ctrlh/solder-alert/firmware/images/btn-nogo.png

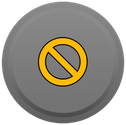
firmware/images/btn-nogo.png
