ctrlh/solder-alert/firmware/images/btn-power-off.png

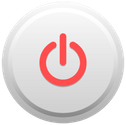
firmware/images/btn-power-off.png
