ctrlh/solder-alert/assembly/full/assembly-01.webp

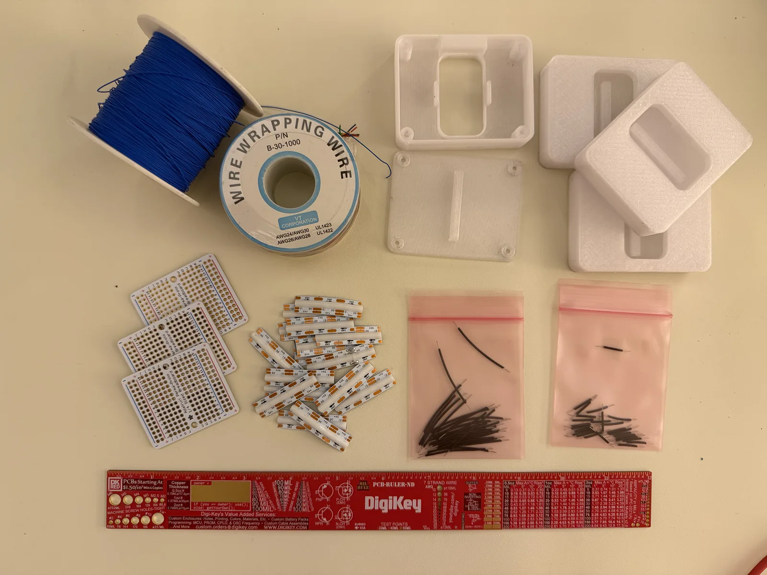
assembly/full/assembly-01.webp
