ctrlh/solder-alert/assembly/full/assembly-02.webp

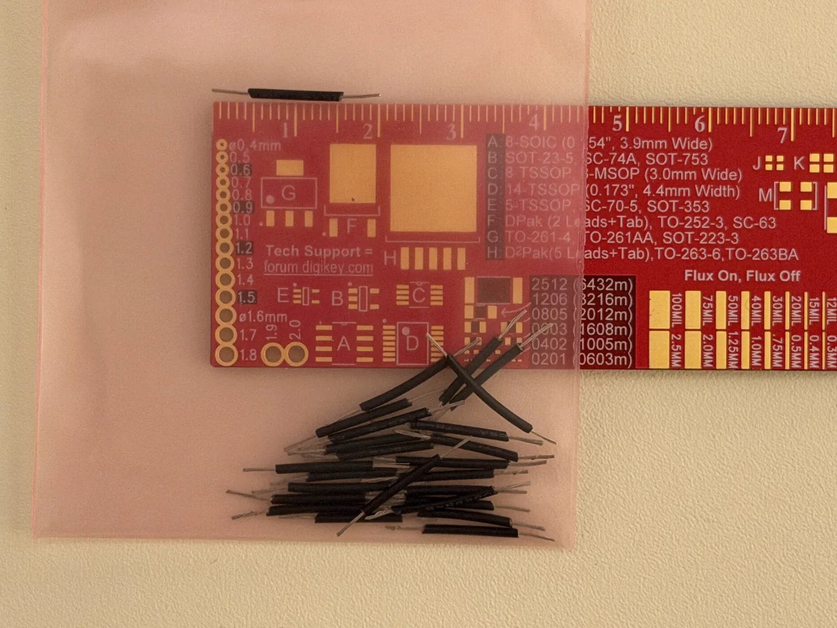
assembly/full/assembly-02.webp
