ctrlh/solder-alert/assembly/full/assembly-03.webp

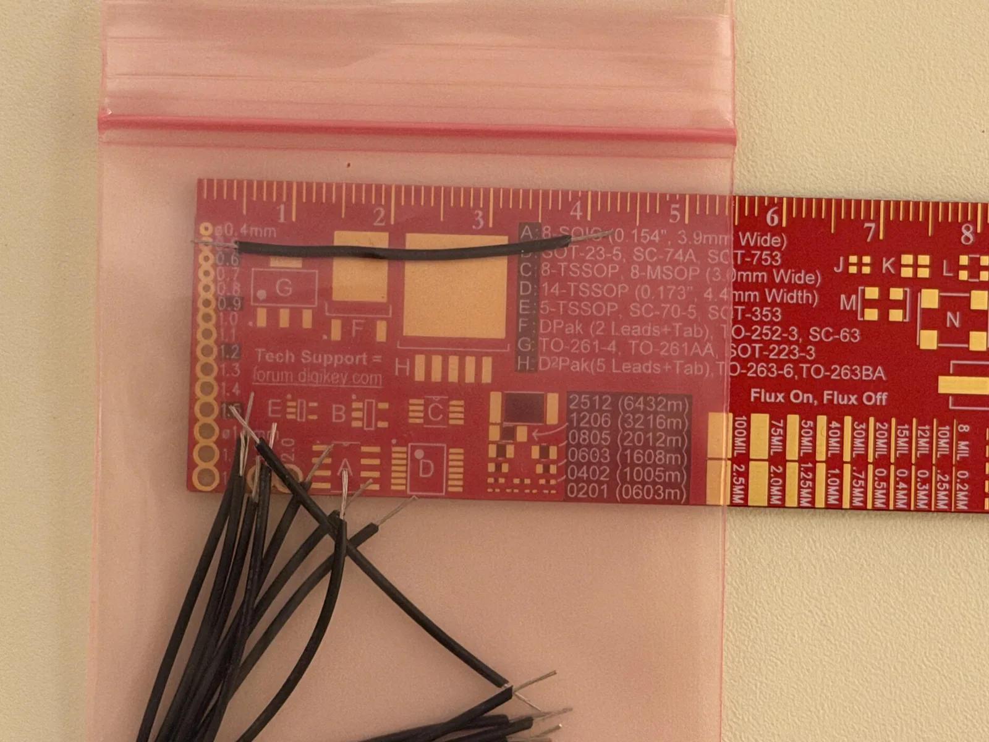
assembly/full/assembly-03.webp
