ctrlh/solder-alert/assembly/full/assembly-05.webp

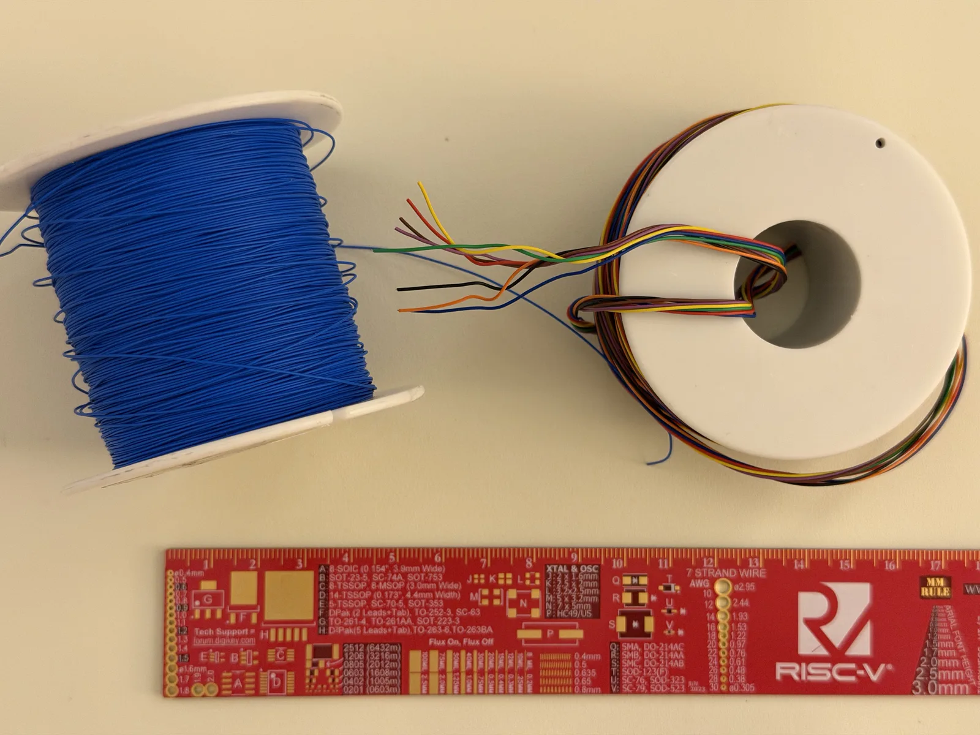
assembly/full/assembly-05.webp
