ctrlh/solder-alert/assembly/full/assembly-06.webp

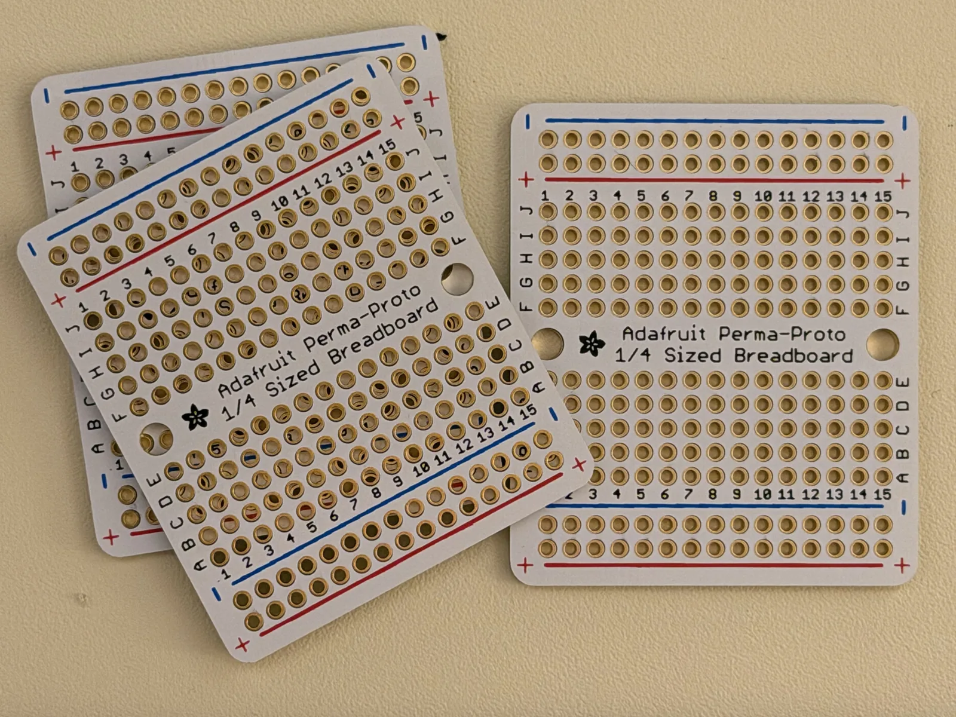
assembly/full/assembly-06.webp
