ctrlh/solder-alert/assembly/full/assembly-07.webp

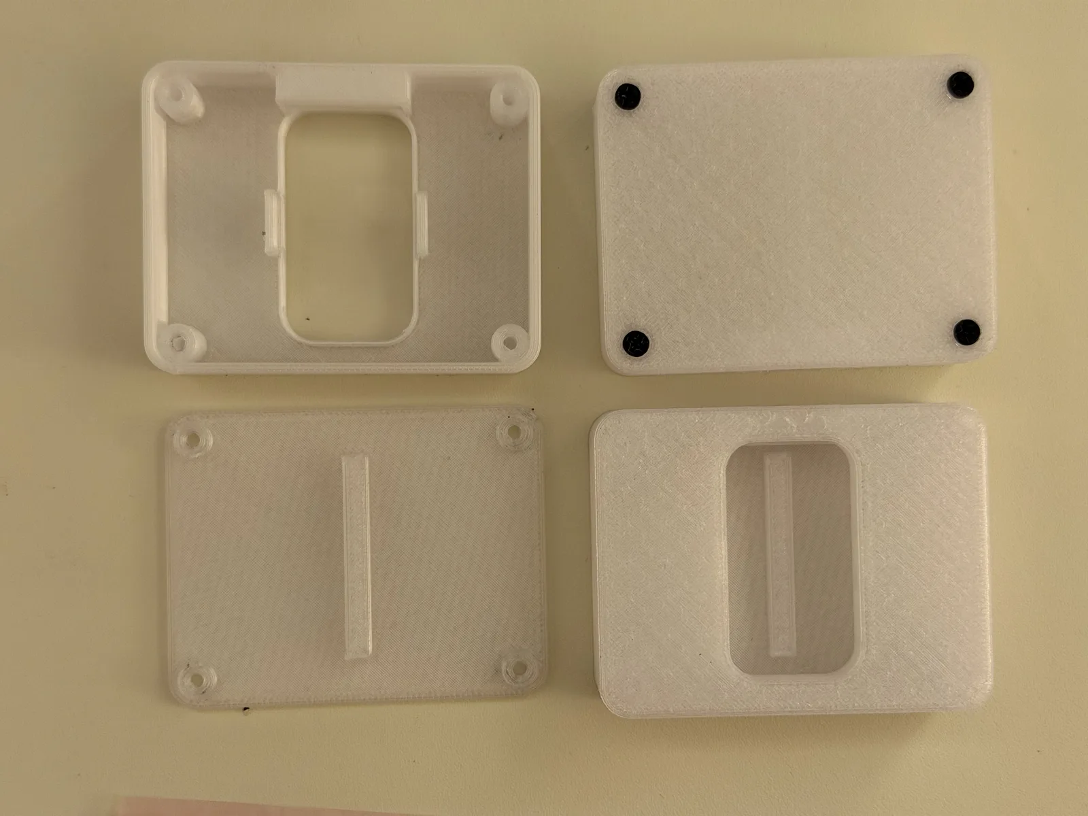
assembly/full/assembly-07.webp
