ctrlh/solder-alert/assembly/full/assembly-08.webp

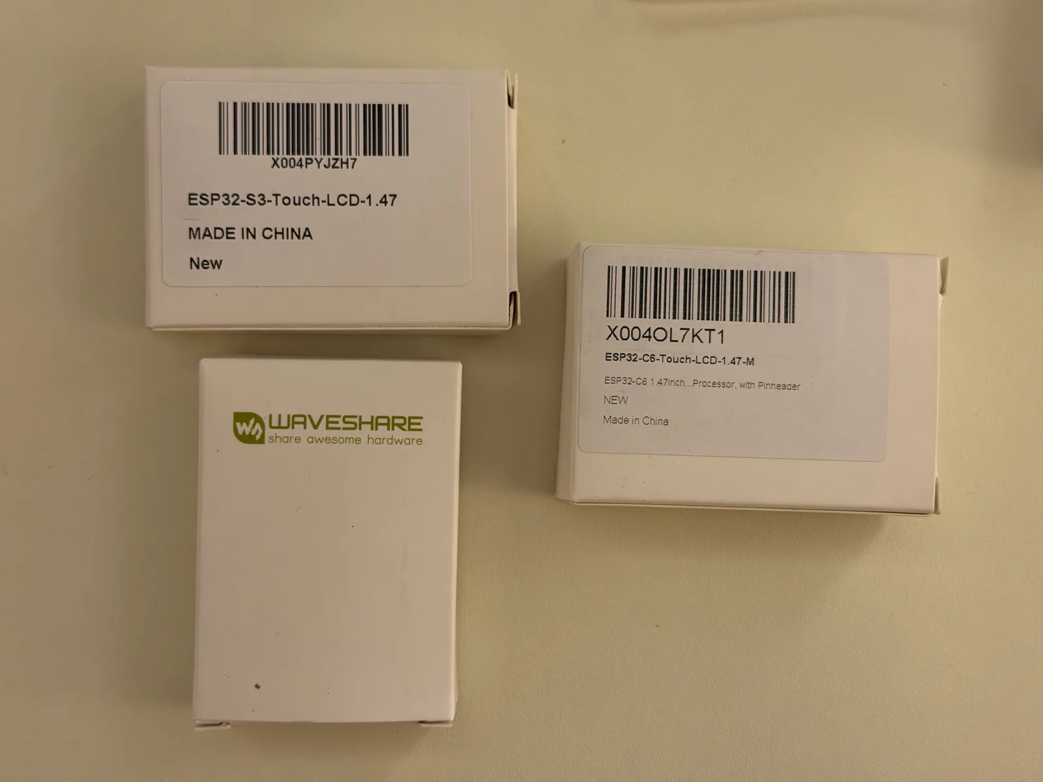
assembly/full/assembly-08.webp
