ctrlh/solder-alert/assembly/full/assembly-09.webp

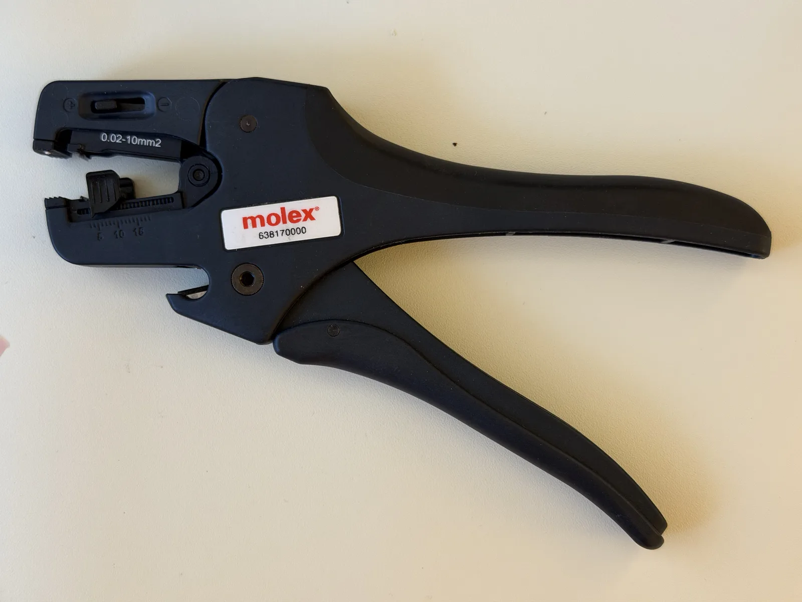
assembly/full/assembly-09.webp
