ctrlh/solder-alert/assembly/full/assembly-10.webp

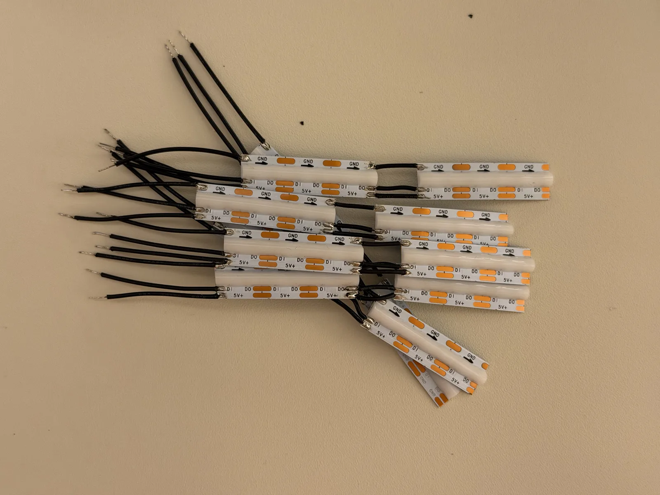
assembly/full/assembly-10.webp
