ctrlh/solder-alert/assembly/full/assembly-11.webp

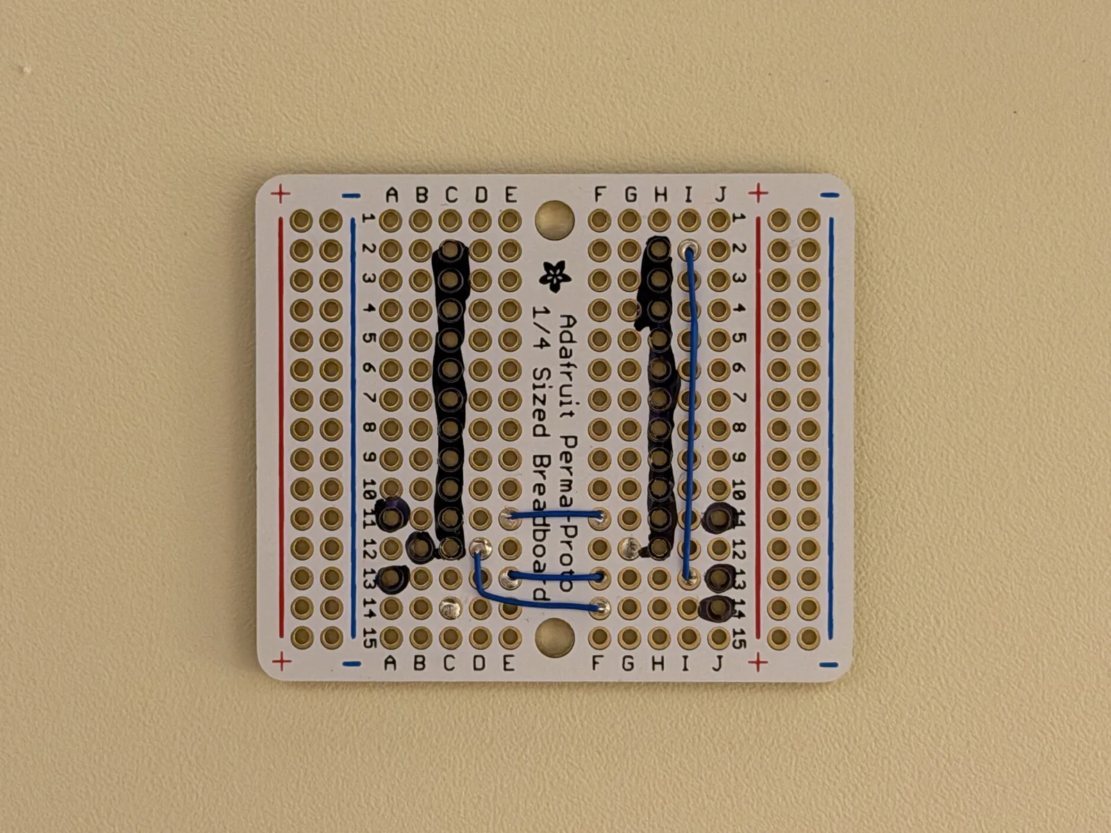
assembly/full/assembly-11.webp
