ctrlh/solder-alert/assembly/full/assembly-12.webp

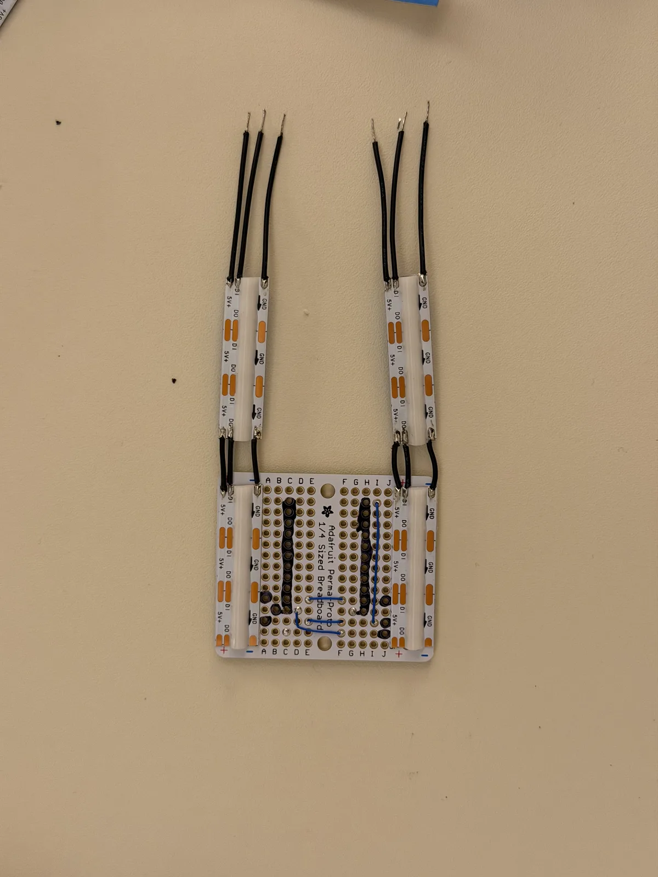
assembly/full/assembly-12.webp
