ctrlh/solder-alert/assembly/full/assembly-14.webp

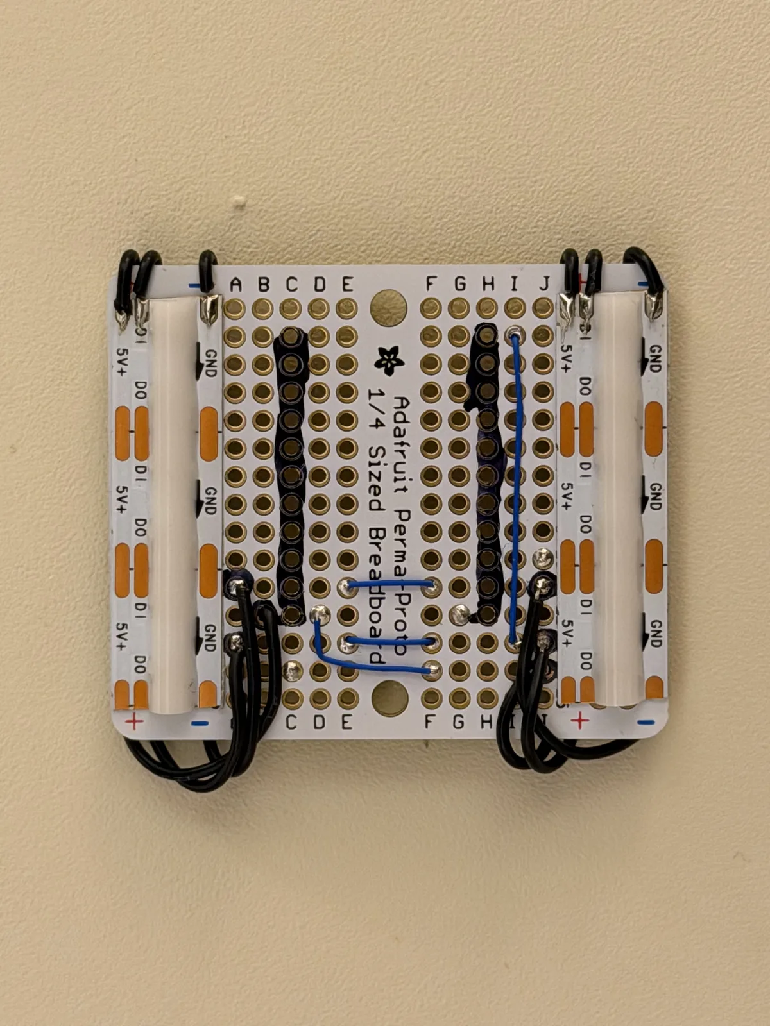
assembly/full/assembly-14.webp
