ctrlh/solder-alert/assembly/full/assembly-17.webp

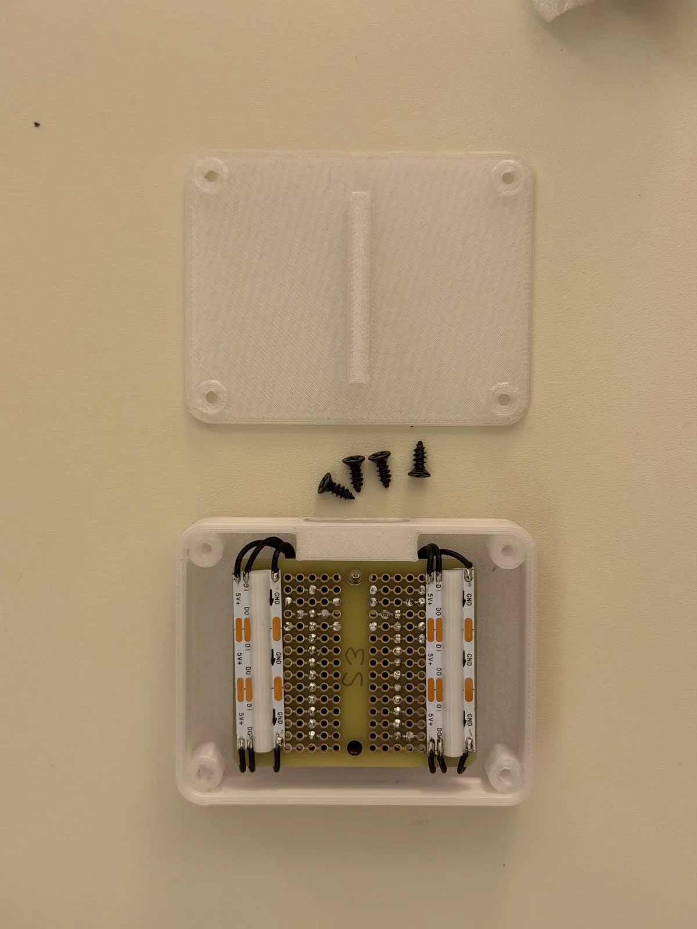
assembly/full/assembly-17.webp
