ctrlh/solder-alert/assembly/full/wire-thickness.webp

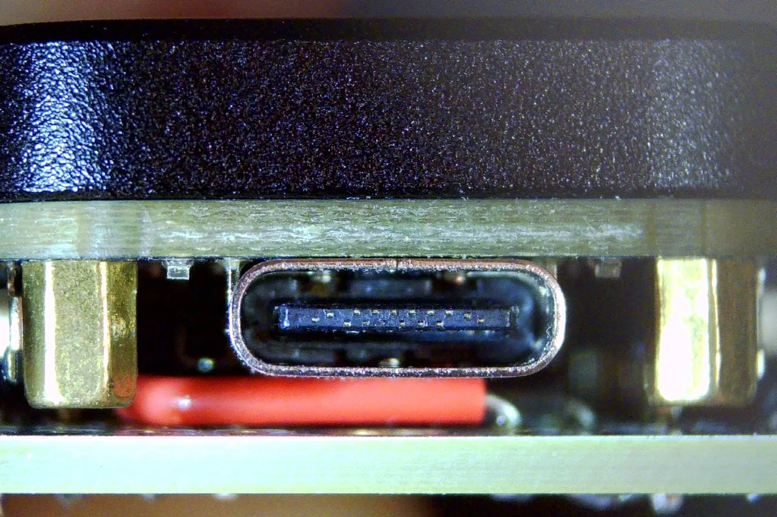
assembly/full/wire-thickness.webp
