ctrlh/solder-alert/assembly/thumb/assembly-12.webp

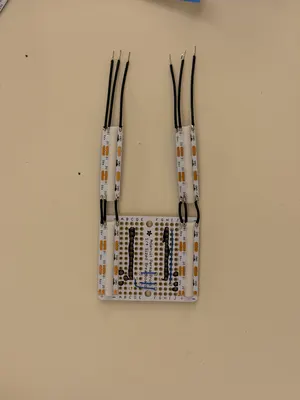
assembly/thumb/assembly-12.webp
