ctrlh/solder-alert/assembly/thumb/assembly-13.webp

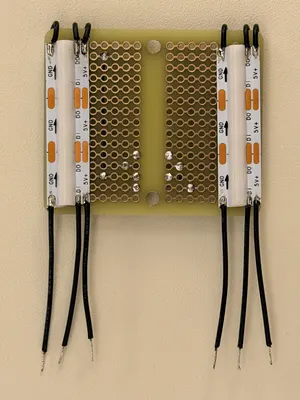
assembly/thumb/assembly-13.webp
