ctrlh/solder-alert/assembly/thumb/assembly-17.webp

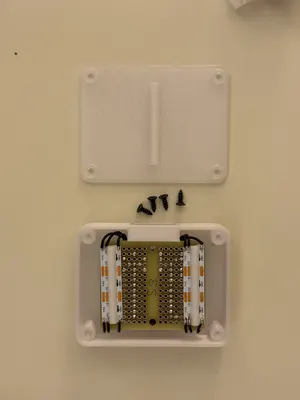
assembly/thumb/assembly-17.webp
